kerokero5150/SP2SD_DIY_KIT/SD2SD_PIX/IMG_6992.jpeg

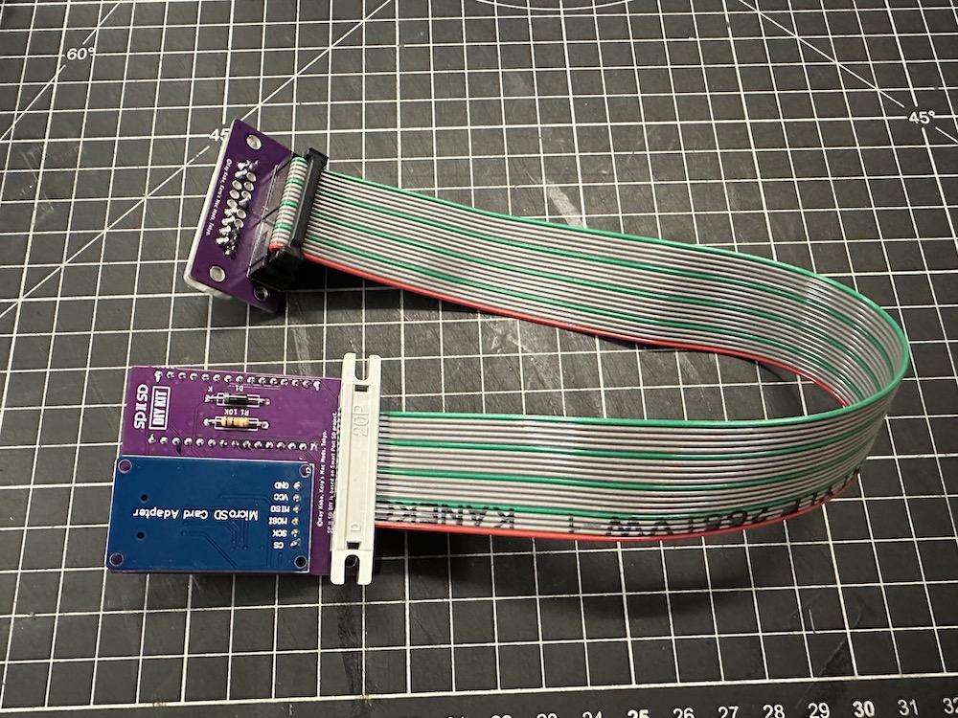
SD2SD_PIX/IMG_6992.jpeg
